zaxour/TurboNanza/images/duo/Bonanza_Audio_Connected.jpg

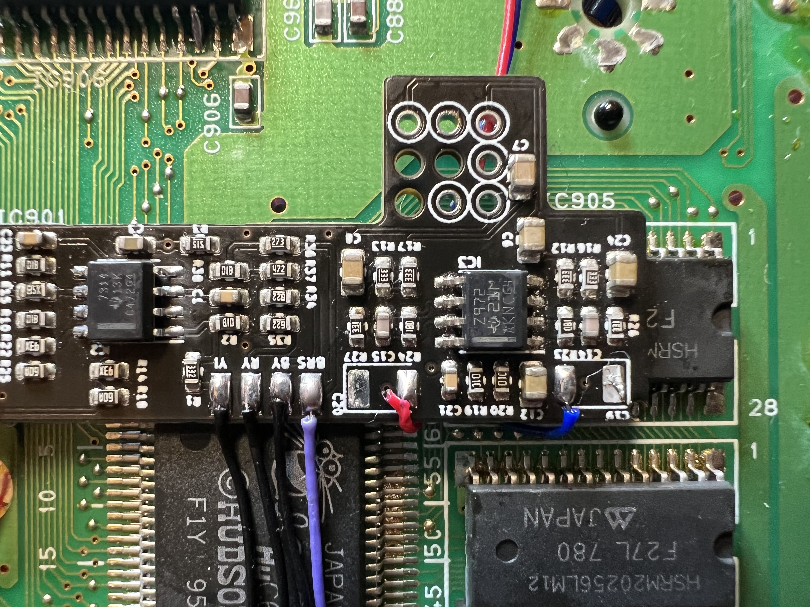
images/duo/Bonanza_Audio_Connected.jpg
