zaxour/TurboNanza/images/duo/BURS_BY_RY_Y.jpg

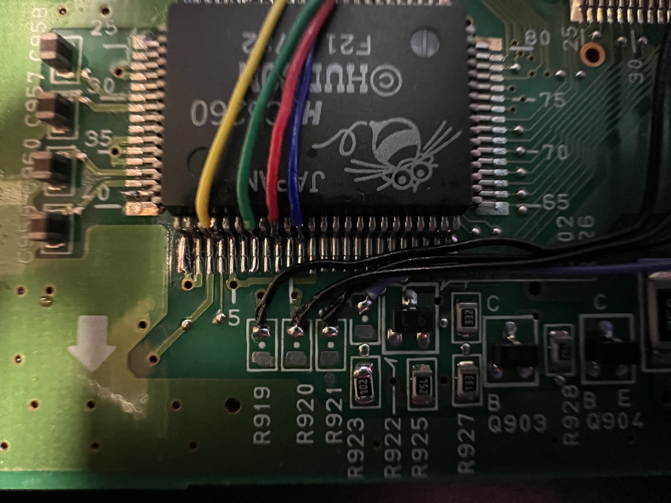
images/duo/BURS_BY_RY_Y.jpg
