zaxour/TurboNanza/images/duo/DIN.jpg

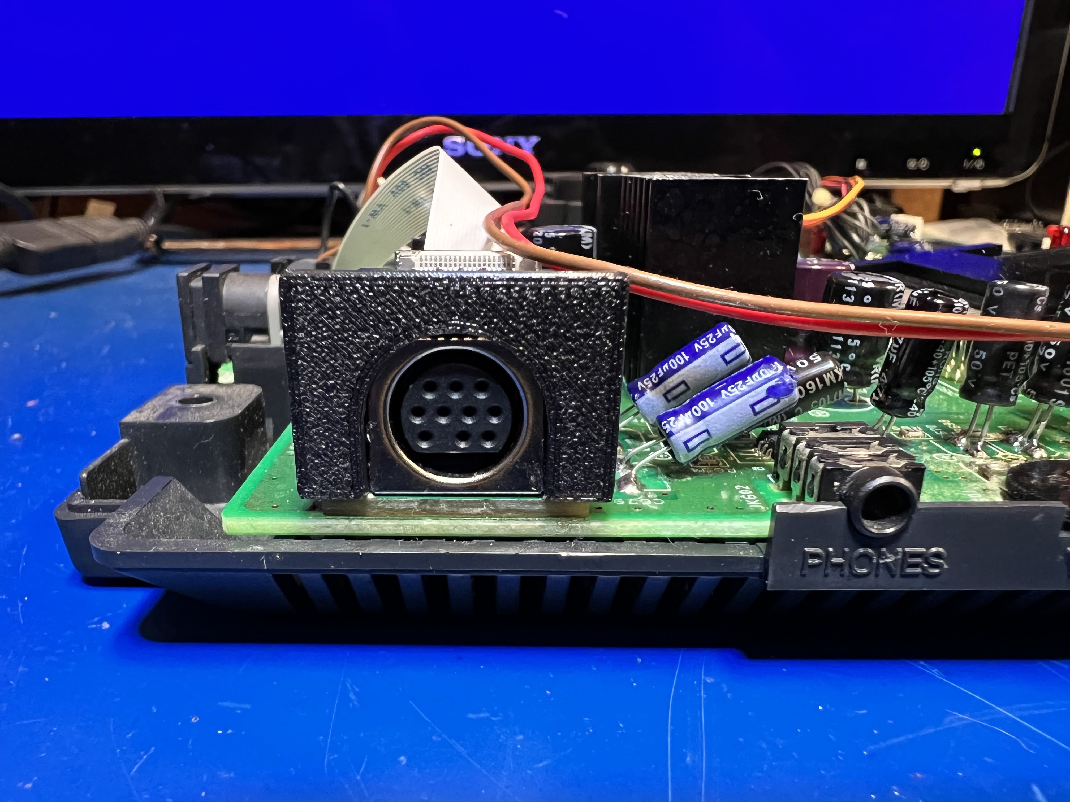
images/duo/DIN.jpg
