zaxour/TurboNanza/images/duo/NewDIN_Caps.jpg

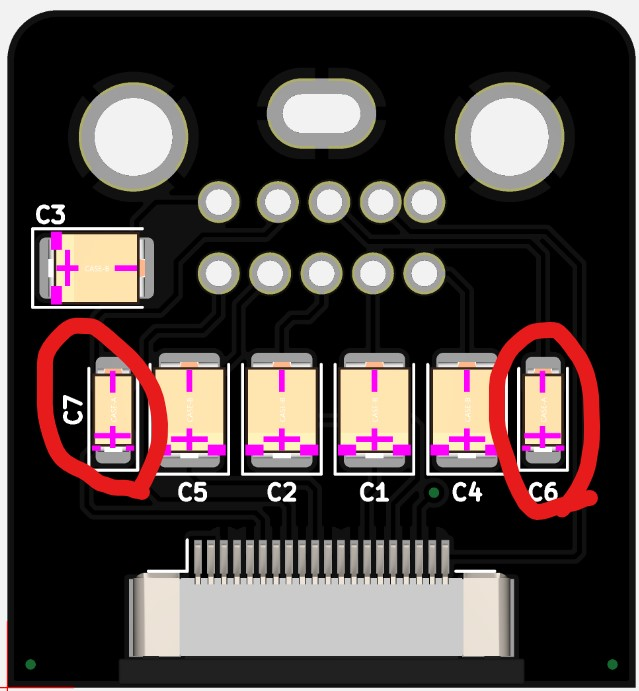
images/duo/NewDIN_Caps.jpg
