zaxour/TurboNanza/images/Assembly Step 1.jpg

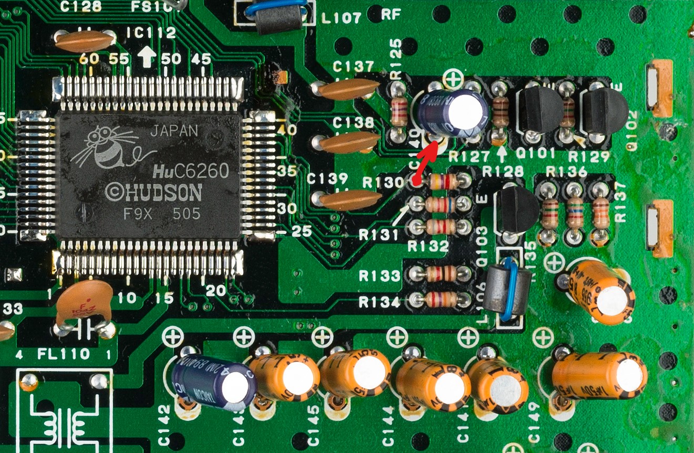
images/Assembly Step 1.jpg
