zaxour/TurboNanza/images/RevC - PCE Step 4 - SV Solder Points.png

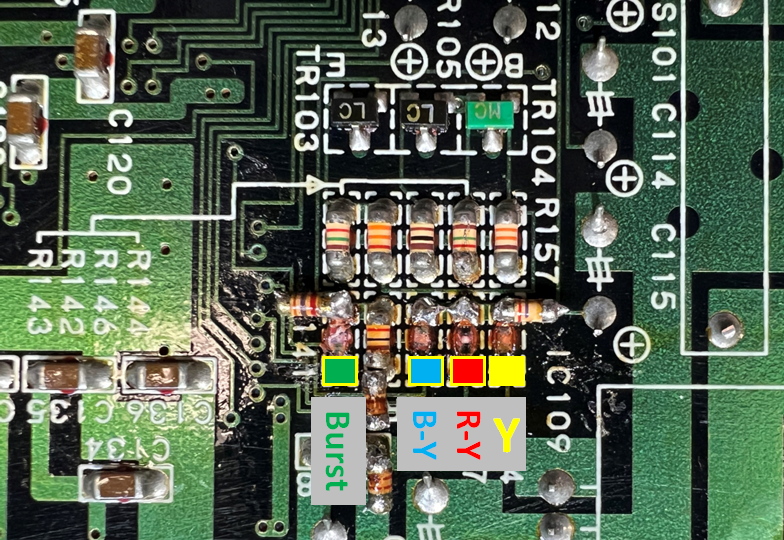
images/RevC - PCE Step 4 - SV Solder Points.png
