zaxour/TurboNanza/images/RevC_CG_Step5D.jpg

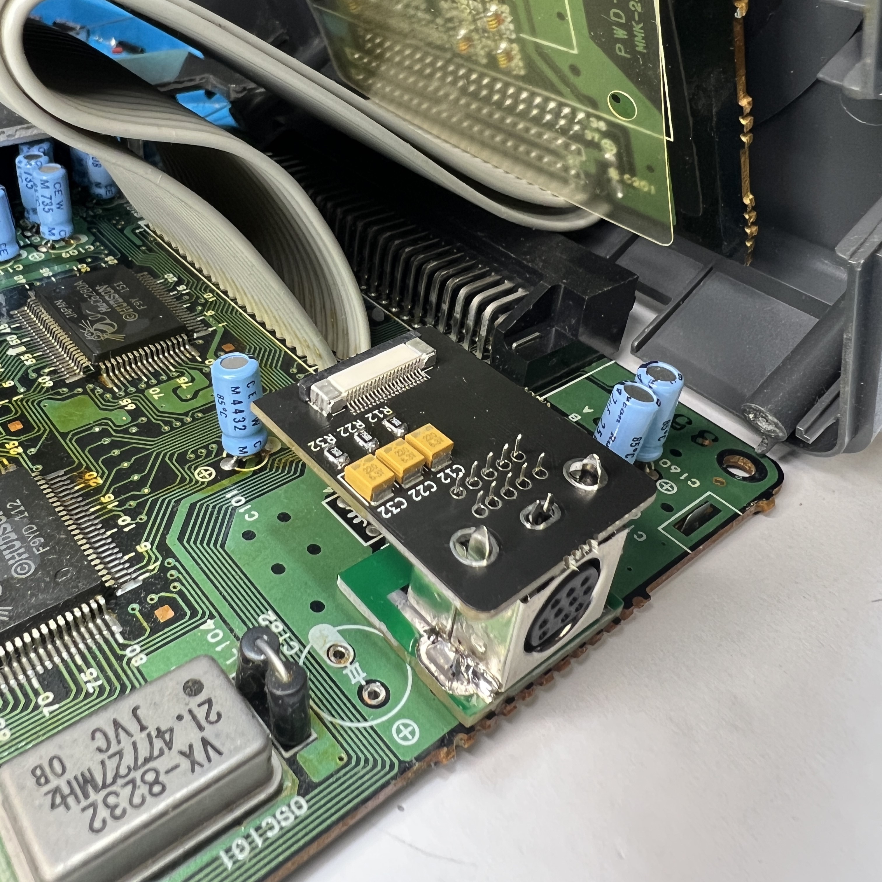
images/RevC_CG_Step5D.jpg
