zaxour/TurboNanza/images/RevC_CG_Step5E.jpg

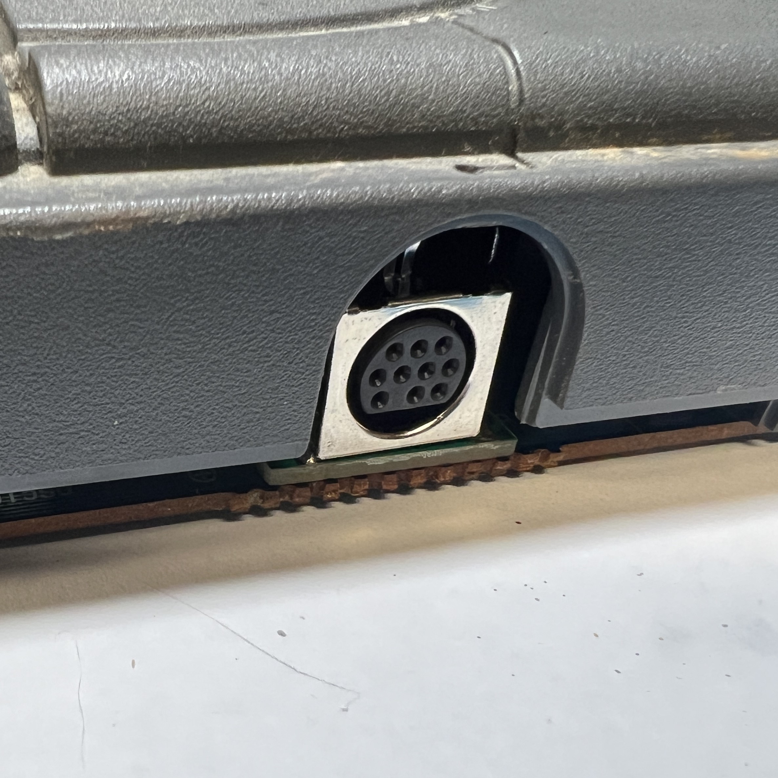
images/RevC_CG_Step5E.jpg
