zaxour/TurboNanza/images/RevC_CG_Step5G.jpg

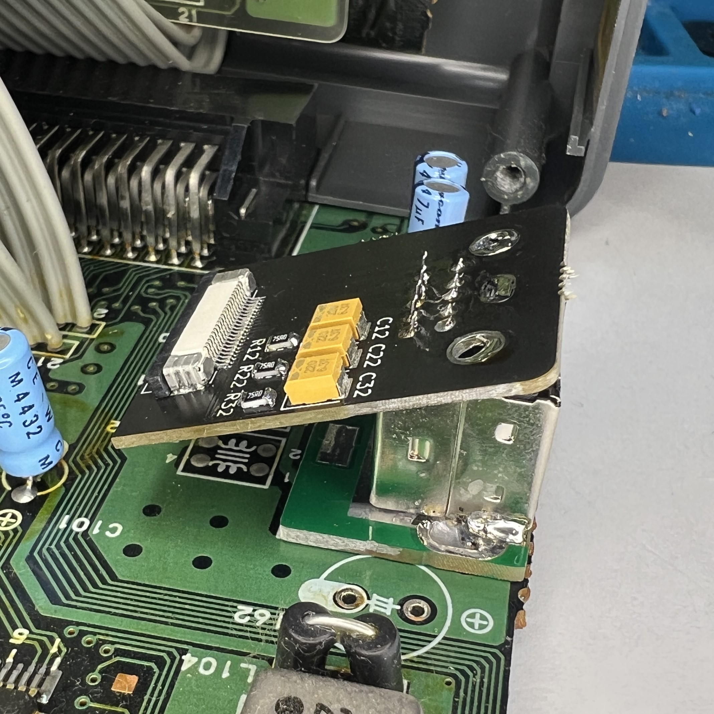
images/RevC_CG_Step5G.jpg
